ronijatkola/Pirkka-R2-D2/electronics/Schematics.kicad_sch

## KiCad design electronics/Schematics.kicad_sch (2025-05-02)

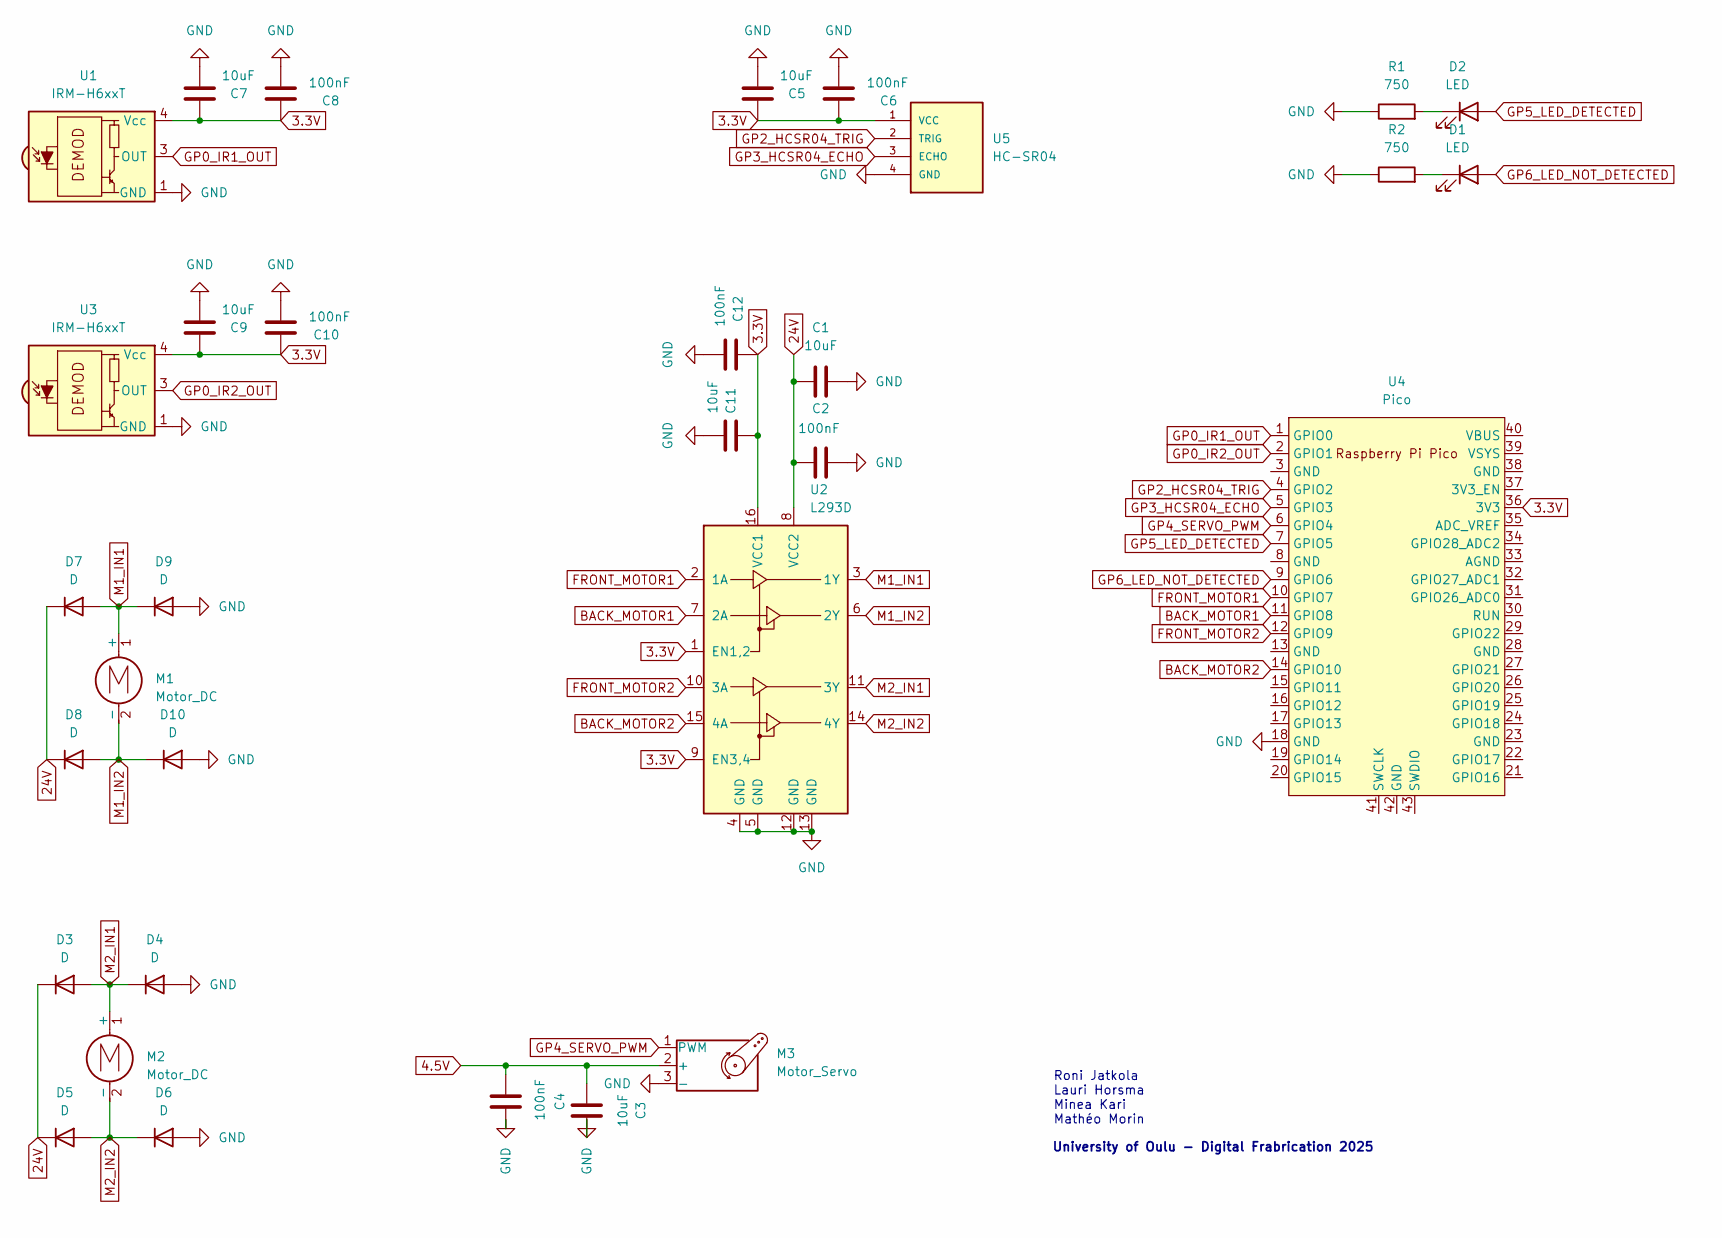
[picture p4: schematic Schematics.kicad_sch]

Parts:
C1, C3, C5, C7, C9, C11: 10uF
C2, C4, C6, C8, C10, C12: 100nF
D1, D2: LED
D3, D4, D5, D6, D7, D8, D9, D10: D
M1, M2: Motor_DC
M3: Motor_Servo
R1, R2: 750
U1, U3: IRM-H6xxT; Everlight_IRM-H6xxT
U2: L293D; DIP-16_W7.62mm
U4: Pico; RPi_Pico_SMD_TH
U5: HC-SR04; XCVR_HC-SR04

Connections:
3.3V: C5.1, C6.1, C7.1, C8.1, C9.1, C10.1, C11.1, C12.1, U1.4 (Vcc), U2.1 (EN1,2), U2.9 (EN3,4), U2.16 (VCC1), U3.4 (Vcc), U4.36 (3V3), U5.1 (VCC)
4.5V: C3.1, C4.2, M3.2 (+)
24V: C1.1, C2.2, D3.1 (K), D5.1 (K), D7.1 (K), D8.1 (K), U2.8 (VCC2)
BACK_MOTOR1: U2.7 (2A), U4.11 (GPIO8)
BACK_MOTOR2: U2.15 (4A), U4.14 (GPIO10)
FRONT_MOTOR1: U2.2 (1A), U4.10 (GPIO7)
FRONT_MOTOR2: U2.10 (3A), U4.12 (GPIO9)
GND: C1.2, C2.1, C3.2, C4.1, C5.2, C6.2, C7.2, C8.2, C9.2, C10.2, C11.2, C12.2, D4.2 (A), D6.2 (A), D9.2 (A), D10.2 (A), M3.3 (-), R1.1, R2.1, U1.1 (GND), U1.2 (GND), U2.4 (GND), U2.5 (GND), U2.12 (GND), U2.13 (GND), U3.1 (GND), U3.2 (GND), U4.18 (GND), U5.4 (GND)
GP0_IR1_OUT: U1.3 (OUT), U4.1 (GPIO0)
GP0_IR2_OUT: U3.3 (OUT), U4.2 (GPIO1)
GP2_HCSR04_TRIG: U4.4 (GPIO2), U5.2 (TRIG)
GP3_HCSR04_ECHO: U4.5 (GPIO3), U5.3 (ECHO)
GP4_SERVO_PWM: M3.1 (PWM), U4.6 (GPIO4)
GP5_LED_DETECTED: D2.2 (A), U4.7 (GPIO5)
GP6_LED_NOT_DETECTED: D1.2 (A), U4.9 (GPIO6)
M1_IN1: D7.2 (A), D9.1 (K), M1.1 (+), U2.3 (1Y)
M1_IN2: D8.2 (A), D10.1 (K), M1.2 (-), U2.6 (2Y)
M2_IN1: D3.2 (A), D4.1 (K), M2.1 (+), U2.11 (3Y)
M2_IN2: D5.2 (A), D6.1 (K), M2.2 (-), U2.14 (4Y)
unnamed: D1.1 (K), R2.2
unnamed: D2.1 (K), R1.2

Notes on the sheet:
Roni Jatkola Lauri Horsma Minea Kari Mathéo Morin
University of Oulu - Digital Frabrication 2025
